kb-elmo/twelvekey/firmware/bootloader/updater/updater.asm

updater.elf:     file format elf32-avr

SYMBOL TABLE:
00800100 l    d  .data	00000000 .data
00000000 l    d  .text	00000000 .text
00000000 l    d  .stab	00000000 .stab
00000000 l    d  .stabstr	00000000 .stabstr
00000000 l    d  .comment	00000000 .comment
00000000 l    d  .note.gnu.avr.deviceinfo	00000000 .note.gnu.avr.deviceinfo
00000000 l    d  .debug_info	00000000 .debug_info
00000000 l    d  .debug_abbrev	00000000 .debug_abbrev
00000000 l    d  .debug_line	00000000 .debug_line
00000000 l    d  .debug_str	00000000 .debug_str
00000000 l    df *ABS*	00000000 updater.c
0000003e l       *ABS*	00000000 __SP_H__
0000003d l       *ABS*	00000000 __SP_L__
0000003f l       *ABS*	00000000 __SREG__
00000000 l       *ABS*	00000000 __tmp_reg__
00000001 l       *ABS*	00000000 __zero_reg__
000000b0 l       .text	00000000 loop10
000000de l       .text	00000000 loop27
00000000 l    df *ABS*	00000000 _exit.o
00000c9a l       .text	00000000 __stop_program
0000008e  w      .text	00000000 __vector_22
0000008e  w      .text	00000000 __vector_1
00800100 g     O .data	00000002 new_firmware
00000800 g       *ABS*	00000000 __DATA_REGION_LENGTH__
00000090 g     F .text	0000002e do_spm
00000000 g       *ABS*	00000000 __TEXT_REGION_ORIGIN__
00000aa6 g     F .text	00000012 memcpy_PF
00000068 g       .text	00000000 __trampolines_start
00000c9c g       .text	00000000 _etext
0000008e  w      .text	00000000 __vector_24
0000008e  w      .text	00000000 __vector_12
0000008e g       .text	00000000 __bad_interrupt
00000214 g       .text	00000000 usbasploader
00000c9e g       *ABS*	00000000 __data_load_end
0000008e  w      .text	00000000 __vector_6
00000068 g       .text	00000000 __trampolines_end
0000008e  w      .text	00000000 __vector_3
0000008e  w      .text	00000000 __vector_23
00000c9c g       *ABS*	00000000 __data_load_start
00000068 g       .text	00000000 __dtors_end
00000400 g       *ABS*	00000000 __LOCK_REGION_LENGTH__
0000008e  w      .text	00000000 __vector_25
0000008e  w      .text	00000000 __vector_11
00000068  w      .text	00000000 __init
00000aa6 g       .text	00000000 _binary_usbasploader_raw_end
0000008e  w      .text	00000000 __vector_13
0000008e  w      .text	00000000 __vector_17
0000008e  w      .text	00000000 __vector_19
0000008e  w      .text	00000000 __vector_7
00810000 g       .text	00000000 __eeprom_end
00000000 g       .text	00000000 __vectors
00800102 g       .data	00000000 __data_end
00000892 g       *ABS*	00000000 _binary_usbasploader_raw_size
00000000  w      .text	00000000 __vector_default
0000008e  w      .text	00000000 __vector_5
00000112 g     F .text	00000102 mypgm_WRITEpage
000000ec g     F .text	00000026 mypgm_readpage
00000400 g       *ABS*	00000000 __SIGNATURE_REGION_LENGTH__
00000068 g       .text	00000000 __ctors_start
00000074 g       .text	00000016 .hidden __do_copy_data
00000c8a g     F .text	0000000e memset
00000ab8 g     F .text	000001d2 main
0000008e  w      .text	00000000 __vector_4
00800100 g       *ABS*	00000000 __DATA_REGION_ORIGIN__
00000000  w      *ABS*	00000000 __heap_end
0000008e  w      .text	00000000 __vector_9
0000008e  w      .text	00000000 __vector_2
00000400 g       *ABS*	00000000 __USER_SIGNATURE_REGION_LENGTH__
0000008e  w      .text	00000000 __vector_21
0000008e  w      .text	00000000 __vector_15
00000068 g       .text	00000000 __dtors_start
00000068 g       .text	00000000 __ctors_end
000008ff  w      *ABS*	00000000 __stack
00800102 g       .data	00000000 _edata
00800102 g       .text	00000000 _end
0000008e  w      .text	00000000 __vector_8
00000c98  w      .text	00000000 .hidden exit
00000400 g       *ABS*	00000000 __EEPROM_REGION_LENGTH__
00000c98 g       .text	00000000 .hidden _exit
0000008e  w      .text	00000000 __vector_14
000000be g     F .text	0000002e temp_do_spm
0000008e  w      .text	00000000 __vector_10
0000008e  w      .text	00000000 __vector_16
00800100 g       .data	00000000 __data_start
0000008e  w      .text	00000000 __vector_18
00000003 g       *ABS*	00000000 __FUSE_REGION_LENGTH__
00008000 g       *ABS*	00000000 __TEXT_REGION_LENGTH__
0000008e  w      .text	00000000 __vector_20



Disassembly of section .text:

00000000 <__vectors>:
   0:	33 c0       	rjmp	.+102    	; 0x68 <__ctors_end>
   2:	00 00       	nop
   4:	44 c0       	rjmp	.+136    	; 0x8e <__bad_interrupt>
   6:	00 00       	nop
   8:	42 c0       	rjmp	.+132    	; 0x8e <__bad_interrupt>
   a:	00 00       	nop
   c:	40 c0       	rjmp	.+128    	; 0x8e <__bad_interrupt>
   e:	00 00       	nop
  10:	3e c0       	rjmp	.+124    	; 0x8e <__bad_interrupt>
  12:	00 00       	nop
  14:	3c c0       	rjmp	.+120    	; 0x8e <__bad_interrupt>
  16:	00 00       	nop
  18:	3a c0       	rjmp	.+116    	; 0x8e <__bad_interrupt>
  1a:	00 00       	nop
  1c:	38 c0       	rjmp	.+112    	; 0x8e <__bad_interrupt>
  1e:	00 00       	nop
  20:	36 c0       	rjmp	.+108    	; 0x8e <__bad_interrupt>
  22:	00 00       	nop
  24:	34 c0       	rjmp	.+104    	; 0x8e <__bad_interrupt>
  26:	00 00       	nop
  28:	32 c0       	rjmp	.+100    	; 0x8e <__bad_interrupt>
  2a:	00 00       	nop
  2c:	30 c0       	rjmp	.+96     	; 0x8e <__bad_interrupt>
  2e:	00 00       	nop
  30:	2e c0       	rjmp	.+92     	; 0x8e <__bad_interrupt>
  32:	00 00       	nop
  34:	2c c0       	rjmp	.+88     	; 0x8e <__bad_interrupt>
  36:	00 00       	nop
  38:	2a c0       	rjmp	.+84     	; 0x8e <__bad_interrupt>
  3a:	00 00       	nop
  3c:	28 c0       	rjmp	.+80     	; 0x8e <__bad_interrupt>
  3e:	00 00       	nop
  40:	26 c0       	rjmp	.+76     	; 0x8e <__bad_interrupt>
  42:	00 00       	nop
  44:	24 c0       	rjmp	.+72     	; 0x8e <__bad_interrupt>
  46:	00 00       	nop
  48:	22 c0       	rjmp	.+68     	; 0x8e <__bad_interrupt>
  4a:	00 00       	nop
  4c:	20 c0       	rjmp	.+64     	; 0x8e <__bad_interrupt>
  4e:	00 00       	nop
  50:	1e c0       	rjmp	.+60     	; 0x8e <__bad_interrupt>
  52:	00 00       	nop
  54:	1c c0       	rjmp	.+56     	; 0x8e <__bad_interrupt>
  56:	00 00       	nop
  58:	1a c0       	rjmp	.+52     	; 0x8e <__bad_interrupt>
  5a:	00 00       	nop
  5c:	18 c0       	rjmp	.+48     	; 0x8e <__bad_interrupt>
  5e:	00 00       	nop
  60:	16 c0       	rjmp	.+44     	; 0x8e <__bad_interrupt>
  62:	00 00       	nop
  64:	14 c0       	rjmp	.+40     	; 0x8e <__bad_interrupt>
	...

00000068 <__ctors_end>:
  68:	11 24       	eor	r1, r1
  6a:	1f be       	out	0x3f, r1	; 63
  6c:	cf ef       	ldi	r28, 0xFF	; 255
  6e:	d8 e0       	ldi	r29, 0x08	; 8
  70:	de bf       	out	0x3e, r29	; 62
  72:	cd bf       	out	0x3d, r28	; 61

00000074 <__do_copy_data>:
  74:	11 e0       	ldi	r17, 0x01	; 1
  76:	a0 e0       	ldi	r26, 0x00	; 0
  78:	b1 e0       	ldi	r27, 0x01	; 1
  7a:	ec e9       	ldi	r30, 0x9C	; 156
  7c:	fc e0       	ldi	r31, 0x0C	; 12
  7e:	02 c0       	rjmp	.+4      	; 0x84 <__do_copy_data+0x10>
  80:	05 90       	lpm	r0, Z+
  82:	0d 92       	st	X+, r0
  84:	a2 30       	cpi	r26, 0x02	; 2
  86:	b1 07       	cpc	r27, r17
  88:	d9 f7       	brne	.-10     	; 0x80 <__do_copy_data+0xc>
  8a:	16 d5       	rcall	.+2604   	; 0xab8 <main>
  8c:	05 c6       	rjmp	.+3082   	; 0xc98 <_exit>

0000008e <__bad_interrupt>:
  8e:	b8 cf       	rjmp	.-144    	; 0x0 <__vectors>

00000090 <do_spm>:
      );												\
  })
#endif

#if (!(defined(BOOTLOADER_ADDRESS))) || (defined(NEW_BOOTLOADER_ADDRESS))
void do_spm(const uint32_t flash_byteaddress, const uint8_t spmcrval, const uint16_t dataword) {
  90:	bf 92       	push	r11
  92:	cf 92       	push	r12
  94:	df 92       	push	r13
  96:	d9 01       	movw	r26, r18
    __do_spm_Ex(flash_byteaddress, spmcrval, dataword, funcaddr___bootloader__do_spm >> 1);
  98:	e4 e3       	ldi	r30, 0x34	; 52
  9a:	f8 e3       	ldi	r31, 0x38	; 56
  9c:	0f 92       	push	r0
  9e:	1f 92       	push	r1
  a0:	d7 2e       	mov	r13, r23
  a2:	c6 2e       	mov	r12, r22
  a4:	b8 2e       	mov	r11, r24
  a6:	24 2f       	mov	r18, r20
  a8:	1b 2e       	mov	r1, r27
  aa:	0a 2e       	mov	r0, r26
  ac:	09 95       	icall
  ae:	21 31       	cpi	r18, 0x11	; 17

000000b0 <loop10>:
  b0:	f9 f7       	brne	.-2      	; 0xb0 <loop10>
  b2:	1f 90       	pop	r1
  b4:	0f 90       	pop	r0
}
  b6:	df 90       	pop	r13
  b8:	cf 90       	pop	r12
  ba:	bf 90       	pop	r11
  bc:	08 95       	ret

000000be <temp_do_spm>:
void new_do_spm(const uint32_t flash_byteaddress, const uint8_t spmcrval, const uint16_t dataword) {
    __do_spm_Ex(flash_byteaddress, spmcrval, dataword, NEW_SPM_ADDRESS >> 1);
}
#endif

void temp_do_spm(const uint32_t flash_byteaddress, const uint8_t spmcrval, const uint16_t dataword) {
  be:	bf 92       	push	r11
  c0:	cf 92       	push	r12
  c2:	df 92       	push	r13
  c4:	d9 01       	movw	r26, r18
    __do_spm_Ex(flash_byteaddress, spmcrval, dataword, TEMP_SPM_ADDRESS >> 1);
  c6:	e4 e3       	ldi	r30, 0x34	; 52
  c8:	ff e3       	ldi	r31, 0x3F	; 63
  ca:	0f 92       	push	r0
  cc:	1f 92       	push	r1
  ce:	d7 2e       	mov	r13, r23
  d0:	c6 2e       	mov	r12, r22
  d2:	b8 2e       	mov	r11, r24
  d4:	24 2f       	mov	r18, r20
  d6:	1b 2e       	mov	r1, r27
  d8:	0a 2e       	mov	r0, r26
  da:	09 95       	icall
  dc:	21 31       	cpi	r18, 0x11	; 17

000000de <loop27>:
  de:	f9 f7       	brne	.-2      	; 0xde <loop27>
  e0:	1f 90       	pop	r1
  e2:	0f 90       	pop	r0
}
  e4:	df 90       	pop	r13
  e6:	cf 90       	pop	r12
  e8:	bf 90       	pop	r11
  ea:	08 95       	ret

000000ec <mypgm_readpage>:
  
  return result;
}
#else
// replace it somehow with "memcpy_PF" in order to save some ops...
size_t mypgm_readpage(const mypgm_addr_t byteaddress,const void* buffer, const size_t bufferbytesize) {
  ec:	cf 93       	push	r28
  ee:	df 93       	push	r29
  f0:	fa 01       	movw	r30, r20
  f2:	e9 01       	movw	r28, r18
  size_t	result		= (bufferbytesize < SPM_PAGESIZE)?bufferbytesize:SPM_PAGESIZE;
  f4:	21 38       	cpi	r18, 0x81	; 129
  f6:	31 05       	cpc	r19, r1
  f8:	10 f0       	brcs	.+4      	; 0xfe <mypgm_readpage+0x12>
  fa:	c0 e8       	ldi	r28, 0x80	; 128
  fc:	d0 e0       	ldi	r29, 0x00	; 0
  mypgm_addr_t	pageaddr	= byteaddress - (byteaddress % SPM_PAGESIZE);
  
  mymemcpy_PF((void*)buffer, (uint_farptr_t)pageaddr, result);
  fe:	ab 01       	movw	r20, r22
 100:	bc 01       	movw	r22, r24
 102:	40 78       	andi	r20, 0x80	; 128
 104:	9e 01       	movw	r18, r28
 106:	cf 01       	movw	r24, r30
 108:	ce d4       	rcall	.+2460   	; 0xaa6 <memcpy_PF>
  
  return result;
}
 10a:	ce 01       	movw	r24, r28
 10c:	df 91       	pop	r29
 10e:	cf 91       	pop	r28
 110:	08 95       	ret

00000112 <mypgm_WRITEpage>:
#endif

#ifdef CONFIG_UPDATER_REDUCEWRITES
size_t mypgm_WRITEpage(const mypgm_addr_t byteaddress,const void* buffer, const size_t bufferbytesize, mypgm_spminterface spmfunc) {
 112:	2f 92       	push	r2
 114:	3f 92       	push	r3
 116:	4f 92       	push	r4
 118:	5f 92       	push	r5
 11a:	6f 92       	push	r6
 11c:	7f 92       	push	r7
 11e:	8f 92       	push	r8
 120:	9f 92       	push	r9
 122:	af 92       	push	r10
 124:	bf 92       	push	r11
 126:	cf 92       	push	r12
 128:	df 92       	push	r13
 12a:	ef 92       	push	r14
 12c:	ff 92       	push	r15
 12e:	0f 93       	push	r16
 130:	1f 93       	push	r17
 132:	cf 93       	push	r28
 134:	df 93       	push	r29
  size_t	result		= (bufferbytesize < SPM_PAGESIZE)?bufferbytesize:SPM_PAGESIZE;
 136:	e9 01       	movw	r28, r18
 138:	21 38       	cpi	r18, 0x81	; 129
 13a:	31 05       	cpc	r19, r1
 13c:	10 f0       	brcs	.+4      	; 0x142 <mypgm_WRITEpage+0x30>
 13e:	c0 e8       	ldi	r28, 0x80	; 128
 140:	d0 e0       	ldi	r29, 0x00	; 0
  size_t	pagesize	= result >> 1;
 142:	4e 01       	movw	r8, r28
 144:	96 94       	lsr	r9
 146:	87 94       	ror	r8
  uint16_t	*pagedata	= (void*)buffer;
  mypgm_addr_t	pageaddr_bakup	= byteaddress - (byteaddress % SPM_PAGESIZE);
 148:	6b 01       	movw	r12, r22
 14a:	7c 01       	movw	r14, r24
 14c:	20 e8       	ldi	r18, 0x80	; 128
 14e:	c2 22       	and	r12, r18
 150:	5a 01       	movw	r10, r20
  uint8_t	changed=0, needs_erase=0;
  uint16_t	deeword;
  size_t	i;
  
  // just check, if page needs a rewrite or an erase...
  for (i=0;i<pagesize;i+=1) {
 152:	da 01       	movw	r26, r20
 154:	20 e0       	ldi	r18, 0x00	; 0
 156:	30 e0       	ldi	r19, 0x00	; 0
  size_t	pagesize	= result >> 1;
  uint16_t	*pagedata	= (void*)buffer;
  mypgm_addr_t	pageaddr_bakup	= byteaddress - (byteaddress % SPM_PAGESIZE);
  mypgm_addr_t	pageaddr	= pageaddr_bakup;
  
  uint8_t	changed=0, needs_erase=0;
 158:	60 e0       	ldi	r22, 0x00	; 0
 15a:	70 e0       	ldi	r23, 0x00	; 0
  uint16_t	deeword;
  size_t	i;
  
  // just check, if page needs a rewrite or an erase...
  for (i=0;i<pagesize;i+=1) {
 15c:	28 15       	cp	r18, r8
 15e:	39 05       	cpc	r19, r9
 160:	b9 f0       	breq	.+46     	; 0x190 <mypgm_WRITEpage+0x7e>
#if (FLASHEND > 65535)
    deeword=pgm_read_word_far(pageaddr);
#else
    deeword=pgm_read_word(pageaddr);
 162:	f6 01       	movw	r30, r12
 164:	e4 1b       	sub	r30, r20
 166:	f5 0b       	sbc	r31, r21
 168:	ea 0f       	add	r30, r26
 16a:	fb 1f       	adc	r31, r27
 16c:	85 91       	lpm	r24, Z+
 16e:	94 91       	lpm	r25, Z
#endif

    if (deeword != pagedata[i]) changed=1;
 170:	ed 91       	ld	r30, X+
 172:	fd 91       	ld	r31, X+
 174:	8e 17       	cp	r24, r30
 176:	9f 07       	cpc	r25, r31
 178:	09 f0       	breq	.+2      	; 0x17c <mypgm_WRITEpage+0x6a>
 17a:	71 e0       	ldi	r23, 0x01	; 1
     *  0 ? 0 ==> 1
     * 
     * ==> /(/x * y) ==> x + /y
     */
    deeword |= ~pagedata[i];
    if ((~deeword) != 0) needs_erase=1;
 17c:	e0 95       	com	r30
 17e:	f0 95       	com	r31
 180:	8e 2b       	or	r24, r30
 182:	9f 2b       	or	r25, r31
 184:	01 96       	adiw	r24, 0x01	; 1
 186:	09 f0       	breq	.+2      	; 0x18a <mypgm_WRITEpage+0x78>
 188:	61 e0       	ldi	r22, 0x01	; 1
  uint8_t	changed=0, needs_erase=0;
  uint16_t	deeword;
  size_t	i;
  
  // just check, if page needs a rewrite or an erase...
  for (i=0;i<pagesize;i+=1) {
 18a:	2f 5f       	subi	r18, 0xFF	; 255
 18c:	3f 4f       	sbci	r19, 0xFF	; 255
 18e:	e6 cf       	rjmp	.-52     	; 0x15c <mypgm_WRITEpage+0x4a>
    if ((~deeword) != 0) needs_erase=1;
      
    pageaddr+=2;
  }

  if (changed) {
 190:	77 23       	and	r23, r23
 192:	51 f1       	breq	.+84     	; 0x1e8 <mypgm_WRITEpage+0xd6>
 194:	18 01       	movw	r2, r16
    
    if (needs_erase) {
 196:	66 23       	and	r22, r22
 198:	39 f0       	breq	.+14     	; 0x1a8 <mypgm_WRITEpage+0x96>
      //do a page-erase, ATTANTION: flash only can be erased a limited number of times !
      spmfunc(pageaddr_bakup, updater_pageerasecode, 0);
 19a:	20 e0       	ldi	r18, 0x00	; 0
 19c:	30 e0       	ldi	r19, 0x00	; 0
 19e:	43 e0       	ldi	r20, 0x03	; 3
 1a0:	c7 01       	movw	r24, r14
 1a2:	b6 01       	movw	r22, r12
 1a4:	f8 01       	movw	r30, r16
 1a6:	09 95       	icall
  size_t	pagesize	= result >> 1;
  uint16_t	*pagedata	= (void*)buffer;
  mypgm_addr_t	pageaddr_bakup	= byteaddress - (byteaddress % SPM_PAGESIZE);
  mypgm_addr_t	pageaddr	= pageaddr_bakup;
  
  uint8_t	changed=0, needs_erase=0;
 1a8:	26 01       	movw	r4, r12
 1aa:	37 01       	movw	r6, r14
 1ac:	00 e0       	ldi	r16, 0x00	; 0
 1ae:	10 e0       	ldi	r17, 0x00	; 0
    
    // from now on, the page is assumed empty !! (hopefully our code is located somewhere else!)
    // now, fill the tempoary buffer
    // ATTANTION: see comment on "do_spm" !
    pageaddr	= pageaddr_bakup;
    for (i=0;i<pagesize;i+=1) {
 1b0:	08 15       	cp	r16, r8
 1b2:	19 05       	cpc	r17, r9
 1b4:	89 f0       	breq	.+34     	; 0x1d8 <mypgm_WRITEpage+0xc6>
      spmfunc(pageaddr, updater_pagefillcode, pagedata[i]);
 1b6:	f5 01       	movw	r30, r10
 1b8:	21 91       	ld	r18, Z+
 1ba:	31 91       	ld	r19, Z+
 1bc:	5f 01       	movw	r10, r30
 1be:	41 e0       	ldi	r20, 0x01	; 1
 1c0:	c3 01       	movw	r24, r6
 1c2:	b2 01       	movw	r22, r4
 1c4:	f1 01       	movw	r30, r2
 1c6:	09 95       	icall
      pageaddr+=2;
 1c8:	f2 e0       	ldi	r31, 0x02	; 2
 1ca:	4f 0e       	add	r4, r31
 1cc:	51 1c       	adc	r5, r1
 1ce:	61 1c       	adc	r6, r1
 1d0:	71 1c       	adc	r7, r1
    
    // from now on, the page is assumed empty !! (hopefully our code is located somewhere else!)
    // now, fill the tempoary buffer
    // ATTANTION: see comment on "do_spm" !
    pageaddr	= pageaddr_bakup;
    for (i=0;i<pagesize;i+=1) {
 1d2:	0f 5f       	subi	r16, 0xFF	; 255
 1d4:	1f 4f       	sbci	r17, 0xFF	; 255
 1d6:	ec cf       	rjmp	.-40     	; 0x1b0 <mypgm_WRITEpage+0x9e>
      spmfunc(pageaddr, updater_pagefillcode, pagedata[i]);
      pageaddr+=2;
    }
    
    // so, now finally write the page to the FLASH
    spmfunc(pageaddr_bakup, updater_pagewritecode, 0);
 1d8:	20 e0       	ldi	r18, 0x00	; 0
 1da:	30 e0       	ldi	r19, 0x00	; 0
 1dc:	45 e0       	ldi	r20, 0x05	; 5
 1de:	c7 01       	movw	r24, r14
 1e0:	b6 01       	movw	r22, r12
 1e2:	f1 01       	movw	r30, r2
 1e4:	09 95       	icall
 1e6:	02 c0       	rjmp	.+4      	; 0x1ec <mypgm_WRITEpage+0xda>
  } else {
    // no change - no write...
    result = 0;
 1e8:	c0 e0       	ldi	r28, 0x00	; 0
 1ea:	d0 e0       	ldi	r29, 0x00	; 0
  }
  
  
  return result;
}
 1ec:	ce 01       	movw	r24, r28
 1ee:	df 91       	pop	r29
 1f0:	cf 91       	pop	r28
 1f2:	1f 91       	pop	r17
 1f4:	0f 91       	pop	r16
 1f6:	ff 90       	pop	r15
 1f8:	ef 90       	pop	r14
 1fa:	df 90       	pop	r13
 1fc:	cf 90       	pop	r12
 1fe:	bf 90       	pop	r11
 200:	af 90       	pop	r10
 202:	9f 90       	pop	r9
 204:	8f 90       	pop	r8
 206:	7f 90       	pop	r7
 208:	6f 90       	pop	r6
 20a:	5f 90       	pop	r5
 20c:	4f 90       	pop	r4
 20e:	3f 90       	pop	r3
 210:	2f 90       	pop	r2
 212:	08 95       	ret

00000214 <usbasploader>:
 214:	6b c0       	rjmp	.+214    	; 0x2ec <usbasploader+0xd8>
 216:	00 00       	nop
 218:	aa c0       	rjmp	.+340    	; 0x36e <usbasploader+0x15a>
 21a:	00 00       	nop
 21c:	8e c0       	rjmp	.+284    	; 0x33a <usbasploader+0x126>
 21e:	00 00       	nop
 220:	8c c0       	rjmp	.+280    	; 0x33a <usbasploader+0x126>
 222:	00 00       	nop
 224:	8a c0       	rjmp	.+276    	; 0x33a <usbasploader+0x126>
 226:	00 00       	nop
 228:	88 c0       	rjmp	.+272    	; 0x33a <usbasploader+0x126>
 22a:	00 00       	nop
 22c:	86 c0       	rjmp	.+268    	; 0x33a <usbasploader+0x126>
 22e:	00 00       	nop
 230:	84 c0       	rjmp	.+264    	; 0x33a <usbasploader+0x126>
 232:	00 00       	nop
 234:	82 c0       	rjmp	.+260    	; 0x33a <usbasploader+0x126>
 236:	00 00       	nop
 238:	80 c0       	rjmp	.+256    	; 0x33a <usbasploader+0x126>
 23a:	00 00       	nop
 23c:	7e c0       	rjmp	.+252    	; 0x33a <usbasploader+0x126>
 23e:	00 00       	nop
 240:	7c c0       	rjmp	.+248    	; 0x33a <usbasploader+0x126>
 242:	00 00       	nop
 244:	7a c0       	rjmp	.+244    	; 0x33a <usbasploader+0x126>
 246:	00 00       	nop
 248:	78 c0       	rjmp	.+240    	; 0x33a <usbasploader+0x126>
 24a:	00 00       	nop
 24c:	76 c0       	rjmp	.+236    	; 0x33a <usbasploader+0x126>
 24e:	00 00       	nop
 250:	74 c0       	rjmp	.+232    	; 0x33a <usbasploader+0x126>
 252:	00 00       	nop
 254:	72 c0       	rjmp	.+228    	; 0x33a <usbasploader+0x126>
 256:	00 00       	nop
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
 aac:	05 90       	lpm	r0, Z+
 aae:	0d 92       	st	X+, r0
 ab0:	21 50       	subi	r18, 0x01	; 1
 ab2:	30 40       	sbci	r19, 0x00	; 0
 ab4:	d8 f7       	brcc	.-10     	; 0xaac <memcpy_PF+0x6>
 ab6:	08 95       	ret

00000ab8 <main>:
#include "crccheck.c"
#endif

// #pragma GCC diagnostic ignored "-Wno-pointer-to-int-cast"
int main(void)
{
 ab8:	8f 92       	push	r8
 aba:	9f 92       	push	r9
 abc:	af 92       	push	r10
 abe:	bf 92       	push	r11
 ac0:	cf 92       	push	r12
 ac2:	df 92       	push	r13
 ac4:	ef 92       	push	r14
 ac6:	ff 92       	push	r15
 ac8:	0f 93       	push	r16
 aca:	1f 93       	push	r17
 acc:	cf 93       	push	r28
 ace:	df 93       	push	r29
 ad0:	cd b7       	in	r28, 0x3d	; 61
 ad2:	de b7       	in	r29, 0x3e	; 62
 ad4:	c0 58       	subi	r28, 0x80	; 128
 ad6:	d1 09       	sbc	r29, r1
 ad8:	0f b6       	in	r0, 0x3f	; 63
 ada:	f8 94       	cli
 adc:	de bf       	out	0x3e, r29	; 62
 ade:	0f be       	out	0x3f, r0	; 63
 ae0:	cd bf       	out	0x3d, r28	; 61
    uint32_t crcval;
#endif
    size_t  i;
    uint8_t buffer[SPM_PAGESIZE];
    
    MCUCSR = 0; /* do not care about previous reset - just disable the wdt */
 ae2:	14 be       	out	0x34, r1	; 52
		);
	}
	else
	{
        uint8_t register temp_reg;
		__asm__ __volatile__ (
 ae4:	0f b6       	in	r0, 0x3f	; 63
 ae6:	f8 94       	cli
 ae8:	a8 95       	wdr
 aea:	80 91 60 00 	lds	r24, 0x0060	; 0x800060 <__TEXT_REGION_LENGTH__+0x7f8060>
 aee:	88 61       	ori	r24, 0x18	; 24
 af0:	80 93 60 00 	sts	0x0060, r24	; 0x800060 <__TEXT_REGION_LENGTH__+0x7f8060>
 af4:	10 92 60 00 	sts	0x0060, r1	; 0x800060 <__TEXT_REGION_LENGTH__+0x7f8060>
 af8:	0f be       	out	0x3f, r0	; 63
    wdt_disable();
    cli();
 afa:	f8 94       	cli
    // allow to change the firmware
    if (crcval == ((uint32_t)UPDATECRC32)) {
#endif

    // check if firmware would change...
    buffer[0]=0;
 afc:	19 82       	std	Y+1, r1	; 0x01
 afe:	20 91 00 01 	lds	r18, 0x0100	; 0x800100 <__DATA_REGION_ORIGIN__>
 b02:	30 91 01 01 	lds	r19, 0x0101	; 0x800101 <__DATA_REGION_ORIGIN__+0x1>
      uint16_t a, b;
#if (FLASHEND > 65535)
      a=pgm_read_word_far(FULLCORRECTFLASHADDRESS(&new_firmware[i]));
      b=pgm_read_word_far(NEW_BOOTLOADER_ADDRESS+i);
#else
      a=pgm_read_word(FULLCORRECTFLASHADDRESS(&new_firmware[i]));
 b06:	80 e0       	ldi	r24, 0x00	; 0
 b08:	90 e7       	ldi	r25, 0x70	; 112
 b0a:	f9 01       	movw	r30, r18
 b0c:	65 91       	lpm	r22, Z+
 b0e:	74 91       	lpm	r23, Z
      b=pgm_read_word(NEW_BOOTLOADER_ADDRESS+i);
 b10:	fc 01       	movw	r30, r24
 b12:	45 91       	lpm	r20, Z+
 b14:	54 91       	lpm	r21, Z
#endif
      if (a!=b) {
 b16:	64 17       	cp	r22, r20
 b18:	75 07       	cpc	r23, r21
 b1a:	19 f0       	breq	.+6      	; 0xb22 <main+0x6a>
	buffer[0]=1;
 b1c:	81 e0       	ldi	r24, 0x01	; 1
 b1e:	89 83       	std	Y+1, r24	; 0x01
	break;
 b20:	07 c0       	rjmp	.+14     	; 0xb30 <main+0x78>
 b22:	2e 5f       	subi	r18, 0xFE	; 254
 b24:	3f 4f       	sbci	r19, 0xFF	; 255
 b26:	02 96       	adiw	r24, 0x02	; 2
    if (crcval == ((uint32_t)UPDATECRC32)) {
#endif

    // check if firmware would change...
    buffer[0]=0;
    for (i=0;i<SIZEOF_new_firmware;i+=2) {
 b28:	82 39       	cpi	r24, 0x92	; 146
 b2a:	48 e7       	ldi	r20, 0x78	; 120
 b2c:	94 07       	cpc	r25, r20
 b2e:	69 f7       	brne	.-38     	; 0xb0a <main+0x52>
    }



    // need to change the firmware...
    if (buffer[0]) {
 b30:	89 81       	ldd	r24, Y+1	; 0x01
 b32:	88 23       	and	r24, r24
 b34:	09 f4       	brne	.+2      	; 0xb38 <main+0x80>
 b36:	93 c0       	rjmp	.+294    	; 0xc5e <main+0x1a6>
 b38:	28 e6       	ldi	r18, 0x68	; 104
 b3a:	c2 2e       	mov	r12, r18
 b3c:	20 e7       	ldi	r18, 0x70	; 112
 b3e:	d2 2e       	mov	r13, r18
 b40:	e1 2c       	mov	r14, r1
 b42:	f1 2c       	mov	r15, r1
// replace it somehow with "memcpy_PF" in order to save some ops...
size_t mypgm_readpage(const mypgm_addr_t byteaddress,const void* buffer, const size_t bufferbytesize) {
  size_t	result		= (bufferbytesize < SPM_PAGESIZE)?bufferbytesize:SPM_PAGESIZE;
  mypgm_addr_t	pageaddr	= byteaddress - (byteaddress % SPM_PAGESIZE);
  
  mymemcpy_PF((void*)buffer, (uint_farptr_t)pageaddr, result);
 b44:	b7 01       	movw	r22, r14
 b46:	a6 01       	movw	r20, r12
 b48:	40 78       	andi	r20, 0x80	; 128
 b4a:	20 e8       	ldi	r18, 0x80	; 128
 b4c:	30 e0       	ldi	r19, 0x00	; 0
 b4e:	ce 01       	movw	r24, r28
 b50:	01 96       	adiw	r24, 0x01	; 1
 b52:	a9 df       	rcall	.-174    	; 0xaa6 <memcpy_PF>
    if (buffer[0]) {

      // A
      // copy the current "bootloader__do_spm" to tempoary position via std. "bootloader__do_spm"
      for (i=0;i<TEMP_SPM_BLKSIZE;i+=SPM_PAGESIZE) {
	mypgm_WRITEpage(TEMP_SPM_PAGEADR+i, buffer, mypgm_readpage(funcaddr___bootloader__do_spm+i, buffer, sizeof(buffer)), do_spm);
 b54:	c7 01       	movw	r24, r14
 b56:	b6 01       	movw	r22, r12
 b58:	68 56       	subi	r22, 0x68	; 104
 b5a:	72 4f       	sbci	r23, 0xF2	; 242
 b5c:	8f 4f       	sbci	r24, 0xFF	; 255
 b5e:	9f 4f       	sbci	r25, 0xFF	; 255
 b60:	08 e4       	ldi	r16, 0x48	; 72
 b62:	10 e0       	ldi	r17, 0x00	; 0
 b64:	20 e8       	ldi	r18, 0x80	; 128
 b66:	30 e0       	ldi	r19, 0x00	; 0
 b68:	ae 01       	movw	r20, r28
 b6a:	4f 5f       	subi	r20, 0xFF	; 255
 b6c:	5f 4f       	sbci	r21, 0xFF	; 255
 b6e:	d1 da       	rcall	.-2654   	; 0x112 <mypgm_WRITEpage>
 b70:	80 e8       	ldi	r24, 0x80	; 128
 b72:	c8 0e       	add	r12, r24
 b74:	d1 1c       	adc	r13, r1
 b76:	e1 1c       	adc	r14, r1
 b78:	f1 1c       	adc	r15, r1
    // need to change the firmware...
    if (buffer[0]) {

      // A
      // copy the current "bootloader__do_spm" to tempoary position via std. "bootloader__do_spm"
      for (i=0;i<TEMP_SPM_BLKSIZE;i+=SPM_PAGESIZE) {
 b7a:	48 e6       	ldi	r20, 0x68	; 104
 b7c:	c4 16       	cp	r12, r20
 b7e:	42 e7       	ldi	r20, 0x72	; 114
 b80:	d4 06       	cpc	r13, r20
 b82:	e1 04       	cpc	r14, r1
 b84:	f1 04       	cpc	r15, r1
 b86:	f1 f6       	brne	.-68     	; 0xb44 <main+0x8c>
 b88:	81 2c       	mov	r8, r1
 b8a:	90 e7       	ldi	r25, 0x70	; 112
 b8c:	99 2e       	mov	r9, r25
 b8e:	a1 2c       	mov	r10, r1
 b90:	b1 2c       	mov	r11, r1
 b92:	e1 2c       	mov	r14, r1
 b94:	f1 2c       	mov	r15, r1
      // B
      // start updating the firmware to "NEW_BOOTLOADER_ADDRESS" until at least "TEMP_SPM_BLKSIZE"-bytes after "NEW_SPM_ADDRESS" were written
      // therefore use the tempoary "bootloader__do_spm" (since we most probably will overwrite the default do_spm)
      for (i=0;;i+=SPM_PAGESIZE) {
#ifdef CONFIG_UPDATER_CLEANMEMCLEAR
	memset((void*)buffer, 0xff, sizeof(buffer));
 b96:	40 e8       	ldi	r20, 0x80	; 128
 b98:	50 e0       	ldi	r21, 0x00	; 0
 b9a:	6f ef       	ldi	r22, 0xFF	; 255
 b9c:	70 e0       	ldi	r23, 0x00	; 0
 b9e:	ce 01       	movw	r24, r28
 ba0:	01 96       	adiw	r24, 0x01	; 1
 ba2:	73 d0       	rcall	.+230    	; 0xc8a <memset>
#endif
	mymemcpy_PF((void*)buffer, (uint_farptr_t)(FULLCORRECTFLASHADDRESS(&new_firmware[i])), ((SIZEOF_new_firmware-i)>sizeof(buffer))?sizeof(buffer):(SIZEOF_new_firmware-i));
 ba4:	40 91 00 01 	lds	r20, 0x0100	; 0x800100 <__DATA_REGION_ORIGIN__>
 ba8:	50 91 01 01 	lds	r21, 0x0101	; 0x800101 <__DATA_REGION_ORIGIN__+0x1>
 bac:	4e 0d       	add	r20, r14
 bae:	5f 1d       	adc	r21, r15
 bb0:	05 2e       	mov	r0, r21
 bb2:	00 0c       	add	r0, r0
 bb4:	66 0b       	sbc	r22, r22
 bb6:	77 0b       	sbc	r23, r23
 bb8:	20 e8       	ldi	r18, 0x80	; 128
 bba:	30 e0       	ldi	r19, 0x00	; 0
 bbc:	ce 01       	movw	r24, r28
 bbe:	01 96       	adiw	r24, 0x01	; 1
 bc0:	72 df       	rcall	.-284    	; 0xaa6 <memcpy_PF>
	
	mypgm_WRITEpage(NEW_BOOTLOADER_ADDRESS+i, buffer, sizeof(buffer), temp_do_spm);
 bc2:	0f e5       	ldi	r16, 0x5F	; 95
 bc4:	10 e0       	ldi	r17, 0x00	; 0
 bc6:	20 e8       	ldi	r18, 0x80	; 128
 bc8:	30 e0       	ldi	r19, 0x00	; 0
 bca:	ae 01       	movw	r20, r28
 bcc:	4f 5f       	subi	r20, 0xFF	; 255
 bce:	5f 4f       	sbci	r21, 0xFF	; 255
 bd0:	c5 01       	movw	r24, r10
 bd2:	b4 01       	movw	r22, r8
 bd4:	9e da       	rcall	.-2756   	; 0x112 <mypgm_WRITEpage>
 bd6:	80 e8       	ldi	r24, 0x80	; 128
 bd8:	88 0e       	add	r8, r24
 bda:	91 1c       	adc	r9, r1
 bdc:	a1 1c       	adc	r10, r1
 bde:	b1 1c       	adc	r11, r1
	
	if ((NEW_BOOTLOADER_ADDRESS+i) > (NEW_SPM_ADDRESS+TEMP_SPM_BLKSIZE)) break;
 be0:	40 e8       	ldi	r20, 0x80	; 128
 be2:	e4 16       	cp	r14, r20
 be4:	42 e0       	ldi	r20, 0x02	; 2
 be6:	f4 06       	cpc	r15, r20
 be8:	21 f0       	breq	.+8      	; 0xbf2 <main+0x13a>
      }

      // B
      // start updating the firmware to "NEW_BOOTLOADER_ADDRESS" until at least "TEMP_SPM_BLKSIZE"-bytes after "NEW_SPM_ADDRESS" were written
      // therefore use the tempoary "bootloader__do_spm" (since we most probably will overwrite the default do_spm)
      for (i=0;;i+=SPM_PAGESIZE) {
 bea:	80 e8       	ldi	r24, 0x80	; 128
 bec:	e8 0e       	add	r14, r24
 bee:	f1 1c       	adc	r15, r1
	mymemcpy_PF((void*)buffer, (uint_farptr_t)(FULLCORRECTFLASHADDRESS(&new_firmware[i])), ((SIZEOF_new_firmware-i)>sizeof(buffer))?sizeof(buffer):(SIZEOF_new_firmware-i));
	
	mypgm_WRITEpage(NEW_BOOTLOADER_ADDRESS+i, buffer, sizeof(buffer), temp_do_spm);
	
	if ((NEW_BOOTLOADER_ADDRESS+i) > (NEW_SPM_ADDRESS+TEMP_SPM_BLKSIZE)) break;
      }
 bf0:	d2 cf       	rjmp	.-92     	; 0xb96 <main+0xde>
 bf2:	82 e1       	ldi	r24, 0x12	; 18
 bf4:	c8 2e       	mov	r12, r24
 bf6:	86 e0       	ldi	r24, 0x06	; 6
 bf8:	d8 2e       	mov	r13, r24

      // C
      // continue writeing the new_firmware after "NEW_SPM_ADDRESS+TEMP_SPM_BLKSIZE" this time use the "new_do_spm"
      for (;i<SIZEOF_new_firmware;i+=SPM_PAGESIZE) {
#ifdef CONFIG_UPDATER_CLEANMEMCLEAR
	memset((void*)buffer, 0xff, sizeof(buffer));
 bfa:	40 e8       	ldi	r20, 0x80	; 128
 bfc:	50 e0       	ldi	r21, 0x00	; 0
 bfe:	6f ef       	ldi	r22, 0xFF	; 255
 c00:	70 e0       	ldi	r23, 0x00	; 0
 c02:	ce 01       	movw	r24, r28
 c04:	01 96       	adiw	r24, 0x01	; 1
 c06:	41 d0       	rcall	.+130    	; 0xc8a <memset>
#endif
	mymemcpy_PF((void*)buffer, (uint_farptr_t)(FULLCORRECTFLASHADDRESS(&new_firmware[i])), ((SIZEOF_new_firmware-i)>sizeof(buffer))?sizeof(buffer):(SIZEOF_new_firmware-i));
 c08:	96 01       	movw	r18, r12
 c0a:	41 e8       	ldi	r20, 0x81	; 129
 c0c:	c4 16       	cp	r12, r20
 c0e:	d1 04       	cpc	r13, r1
 c10:	10 f0       	brcs	.+4      	; 0xc16 <main+0x15e>
 c12:	20 e8       	ldi	r18, 0x80	; 128
 c14:	30 e0       	ldi	r19, 0x00	; 0
 c16:	40 91 00 01 	lds	r20, 0x0100	; 0x800100 <__DATA_REGION_ORIGIN__>
 c1a:	50 91 01 01 	lds	r21, 0x0101	; 0x800101 <__DATA_REGION_ORIGIN__+0x1>
 c1e:	4e 0d       	add	r20, r14
 c20:	5f 1d       	adc	r21, r15
 c22:	05 2e       	mov	r0, r21
 c24:	00 0c       	add	r0, r0
 c26:	66 0b       	sbc	r22, r22
 c28:	77 0b       	sbc	r23, r23
 c2a:	ce 01       	movw	r24, r28
 c2c:	01 96       	adiw	r24, 0x01	; 1
 c2e:	3b df       	rcall	.-394    	; 0xaa6 <memcpy_PF>

	mypgm_WRITEpage(NEW_BOOTLOADER_ADDRESS+i, buffer, sizeof(buffer), new_do_spm);
 c30:	b7 01       	movw	r22, r14
 c32:	70 59       	subi	r23, 0x90	; 144
 c34:	80 e0       	ldi	r24, 0x00	; 0
 c36:	90 e0       	ldi	r25, 0x00	; 0
 c38:	08 e4       	ldi	r16, 0x48	; 72
 c3a:	10 e0       	ldi	r17, 0x00	; 0
 c3c:	20 e8       	ldi	r18, 0x80	; 128
 c3e:	30 e0       	ldi	r19, 0x00	; 0
 c40:	ae 01       	movw	r20, r28
 c42:	4f 5f       	subi	r20, 0xFF	; 255
 c44:	5f 4f       	sbci	r21, 0xFF	; 255
 c46:	65 da       	rcall	.-2870   	; 0x112 <mypgm_WRITEpage>
	if ((NEW_BOOTLOADER_ADDRESS+i) > (NEW_SPM_ADDRESS+TEMP_SPM_BLKSIZE)) break;
      }

      // C
      // continue writeing the new_firmware after "NEW_SPM_ADDRESS+TEMP_SPM_BLKSIZE" this time use the "new_do_spm"
      for (;i<SIZEOF_new_firmware;i+=SPM_PAGESIZE) {
 c48:	80 e8       	ldi	r24, 0x80	; 128
 c4a:	e8 0e       	add	r14, r24
 c4c:	f1 1c       	adc	r15, r1
 c4e:	40 e8       	ldi	r20, 0x80	; 128
 c50:	c4 1a       	sub	r12, r20
 c52:	d1 08       	sbc	r13, r1
 c54:	82 e9       	ldi	r24, 0x92	; 146
 c56:	e8 16       	cp	r14, r24
 c58:	88 e0       	ldi	r24, 0x08	; 8
 c5a:	f8 06       	cpc	r15, r24
 c5c:	70 f2       	brcs	.-100    	; 0xbfa <main+0x142>
#if defined(UPDATECRC32)
    }
#endif

    return 0;
}
 c5e:	80 e0       	ldi	r24, 0x00	; 0
 c60:	90 e0       	ldi	r25, 0x00	; 0
 c62:	c0 58       	subi	r28, 0x80	; 128
 c64:	df 4f       	sbci	r29, 0xFF	; 255
 c66:	0f b6       	in	r0, 0x3f	; 63
 c68:	f8 94       	cli
 c6a:	de bf       	out	0x3e, r29	; 62
 c6c:	0f be       	out	0x3f, r0	; 63
 c6e:	cd bf       	out	0x3d, r28	; 61
 c70:	df 91       	pop	r29
 c72:	cf 91       	pop	r28
 c74:	1f 91       	pop	r17
 c76:	0f 91       	pop	r16
 c78:	ff 90       	pop	r15
 c7a:	ef 90       	pop	r14
 c7c:	df 90       	pop	r13
 c7e:	cf 90       	pop	r12
 c80:	bf 90       	pop	r11
 c82:	af 90       	pop	r10
 c84:	9f 90       	pop	r9
 c86:	8f 90       	pop	r8
 c88:	08 95       	ret

00000c8a <memset>:
 c8a:	dc 01       	movw	r26, r24
 c8c:	01 c0       	rjmp	.+2      	; 0xc90 <memset+0x6>
 c8e:	6d 93       	st	X+, r22
 c90:	41 50       	subi	r20, 0x01	; 1
 c92:	50 40       	sbci	r21, 0x00	; 0
 c94:	e0 f7       	brcc	.-8      	; 0xc8e <memset+0x4>
 c96:	08 95       	ret

00000c98 <_exit>:
 c98:	f8 94       	cli

00000c9a <__stop_program>:
 c9a:	ff cf       	rjmp	.-2      	; 0xc9a <__stop_program>
